wjduenow/rivian-status/src/settings.h

// settings — small NVS-backed config the web page edits (plan §8/§9). Distinct from the token/
// dc-cid persistence in rivian_api; this is user-facing config: the low-range threshold (miles)
// and the device/mDNS name.
#pragma once

#include <Arduino.h>

namespace Settings {

void begin();                              // open NVS namespace, load defaults

int  rangeThresholdMiles();                // low-range alert threshold X, in miles (default 50)
void setRangeThresholdMiles(int miles);    // clamped to [1, 500], persisted

int  ledBrightness();                      // LED strip brightness 0-255 (default LED_BRIGHTNESS=40)
void setLedBrightness(int b);              // clamped to [1, 255], persisted

// Physical mounting orientation, expressed the way the user can actually see it: **where the
// USB-C / power lead leaves the case**, as a rotation in degrees clockwise off the natural
// mounting. An outlet's orientation dictates how the device hangs, so all four are realistic.
//   0 = plug at the BOTTOM (natural)   90 = plug at the LEFT
// 180 = plug at the TOP                270 = plug at the RIGHT
// Invariant the firmware maintains: the meter always fills toward screen-**up** when the stick
// lands vertical, and toward screen-**right** when it lands horizontal. leds.cpp compensates.
int  ledRotation();                        // 0 | 90 | 180 | 270 (default 0)
void setLedRotation(int deg);              // snapped to the nearest quarter turn, persisted

// The two things the firmware genuinely cannot know, so they're settings rather than guesses.
// Together with the rotation they pin down the strip completely.
//
// 1. Which AXIS the stick lands on — this differs per enclosure, so plug position alone is not
//    enough. v2 (wall case) holds the stick vertically on the charger's portrait face; v1 (box,
//    board flat to the wall, LEDs facing out) holds it horizontally. Hence: at plug-at-bottom,
//    is the stick vertical?
bool ledStickVertical0();                  // true = v2 wall case, false = v1 box (default)
void setLedStickVertical0(bool vertical);

// 2. Which physical END pixel 0 is. Not derivable — it depends on how the stick was wired into
//    that particular unit. Rather than assume, expose it as a "the meter fills the wrong way"
//    escape hatch: one glance at the device settles it.
bool ledInverted();
void setLedInverted(bool inverted);

bool ledFlipped();                         // derived: does the buffer need reversing?
bool ledVertical();                        // derived: is the stick vertical AS MOUNTED?

String deviceName();                       // DHCP hostname + mDNS + UI title (default DEVICE_HOSTNAME)
void   setDeviceName(const String& name);  // sanitized to DNS-safe, then persisted

// Sanitize to a valid DHCP/mDNS hostname: letters, digits, hyphens; space/underscore -> hyphen;
// no leading/trailing hyphen. "" if nothing usable survives. (Borrowed from sonos-nest.)
String sanitizeHostname(const String& raw);

// Pull-OTA (plan 02 § Phase 2, implemented in net_updater). Checking and applying are separate:
// availability is always reported, but nothing self-flashes unless otaAuto is on or someone
// clicks "Update now".
String updateUrl();                        // "" = AUTO (compiled-in GitHub latest), "off" = never
void   setUpdateUrl(const String& url);    // trimmed; persisted
bool   otaAuto();                          // self-apply a newer build? default FALSE — flashing
void   setOtaAuto(bool on);                // yourself unattended should be opted into, not assumed

// WiFi credentials (NVS). Empty ssid = never provisioned on-device (fall back to secrets.h).
String wifiSsid();
String wifiPass();
void   setWifi(const String& ssid, const String& pass);

} // namespace Settings
