wjduenow/rivian-status/src/rivian_api.h

// rivian_api — the ONLY file that knows Rivian's URLs, headers, and GraphQL strings (plan §8).
// Unofficial, reverse-engineered API; if Rivian changes something, it's fixed here. Sources:
// research/rivian-cloud-api-protocol.md (mined from bretterer/rivian-python-client).
//
// Phase 1 scope: login + getUserInfo + getVehicleState, read-only. No commands, no HMAC, no BLE.
// Tokens live in module statics for the smoke-test; NVS persistence arrives with the `settings`
// module in a later phase. The dc-cid IS persisted now (plan §3/§10) so it's stable from boot one.
#pragma once

#include <Arduino.h>

// Result of a single getVehicleState poll. Every scalar in the API arrives as {timeStamp,value};
// we keep the value plus one timestamp for freshness. `distanceToEmpty` units are UNCONFIRMED
// (km vs miles) — confirming them is a Phase 1 deliverable (plan §6).
struct VehicleStatus {
  bool   valid           = false;
  float  batteryLevel    = NAN;    // charge %, 0-100 — API returns a FLOAT (e.g. 59.700001)
  float  batteryLimit    = NAN;    // charge TARGET % (e.g. 70 or 100) — where charging stops
  String chargerState;             // raw enum, e.g. "charging_active"
  String chargePortState;          // raw enum, e.g. "open"
  float  distanceToEmpty = NAN;    // range in KILOMETERS (§6); firmware converts to miles
  int    timeToEndOfCharge = -1;   // minutes to reach batteryLimit (API int; -1 = unknown)
  String timeStamp;                // timeStamp of batteryLevel
};

namespace RivianApi {

// login() return codes.
enum LoginResult { LOGIN_OK = 0, LOGIN_MFA_REQUIRED = 1, LOGIN_ERROR = -1 };

// One-time init: load-or-generate the persistent dc-cid, load any persisted u-sess, pin the
// Amazon Root CA. Call after WiFi is up and system time is set (TLS needs a real clock).
void begin();

// --- Session persistence (plan §4 reactive model) --------------------------------------------
// After a successful login/OTP the u-sess is auto-saved to NVS. On the next boot, begin() loads
// it, so a reset/reflash can reuse the session (fresh CSRF + stored u-sess) instead of doing the
// whole email/password/MFA dance again. If the stored u-sess has expired, reads fail and the
// caller falls back to a full login, then clears the dead token.
bool hasSession();     // true if a persisted (or freshly obtained) u-sess is loaded
void clearSession();   // wipe the stored u-sess (call when it's confirmed dead)
void seedSession(const String& uSess);  // inject a u-sess obtained out-of-band and persist it
                                         // (restore-from-backup / test bootstrap)

// Step 1: CreateCSRFToken. Populates csrf-token + a-sess. No auth headers.
bool createCsrf();

// Step 2: Login(email,password). LOGIN_OK -> u-sess set; LOGIN_MFA_REQUIRED -> call completeOtp().
LoginResult login(const String& email, const String& password);

// Step 3 (MFA only): LoginWithOTP. Rivian texts the code; caller supplies it. Sets u-sess.
bool completeOtp(const String& email, const String& otpCode);

// getUserInfo -> cache the first vehicle's id + vin + name. Call once after auth.
bool fetchVin();

// getVehicleState for the cached vehicle. Requests only the 4 fields we use (plan §5).
bool pollState(VehicleStatus& out);

// Accessors / diagnostics.
String vin();
String vehicleId();
String vehicleName();
String userSession();   // current u-sess (for dev: copy into SEED_USESS after a fresh login)
String dcCid();
String lastError();   // human-readable last failure
String lastRaw();     // raw body of the last HTTP response (for smoke-test printing)

} // namespace RivianApi
